gowenrw/3k_badge/docs/Code_01.JPG

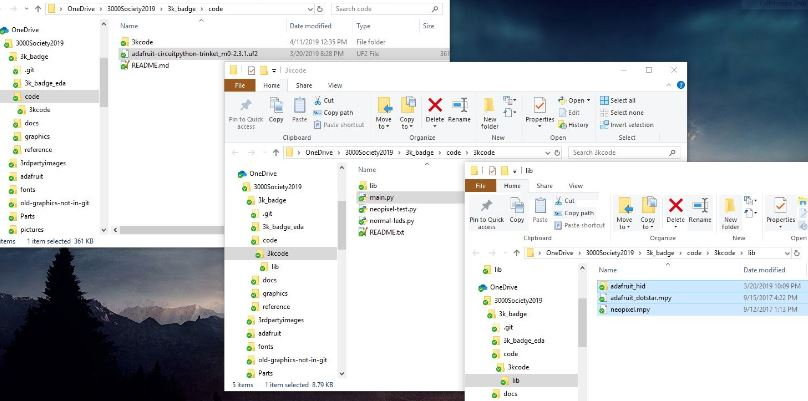
docs/Code_01.JPG
