gowenrw/3k_badge/docs/Code_04.JPG

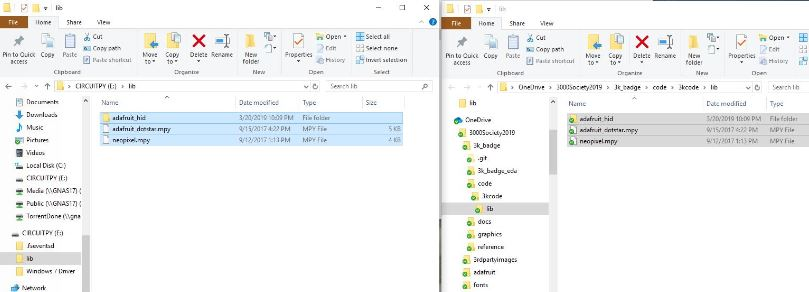
docs/Code_04.JPG
