gowenrw/3k_badge/docs/Code_05.JPG

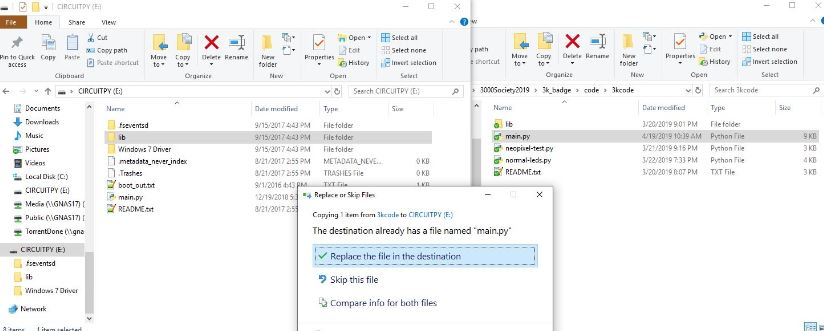
docs/Code_05.JPG
