gowenrw/3k_badge/graphics/3000-white-transparent-full-1080.png

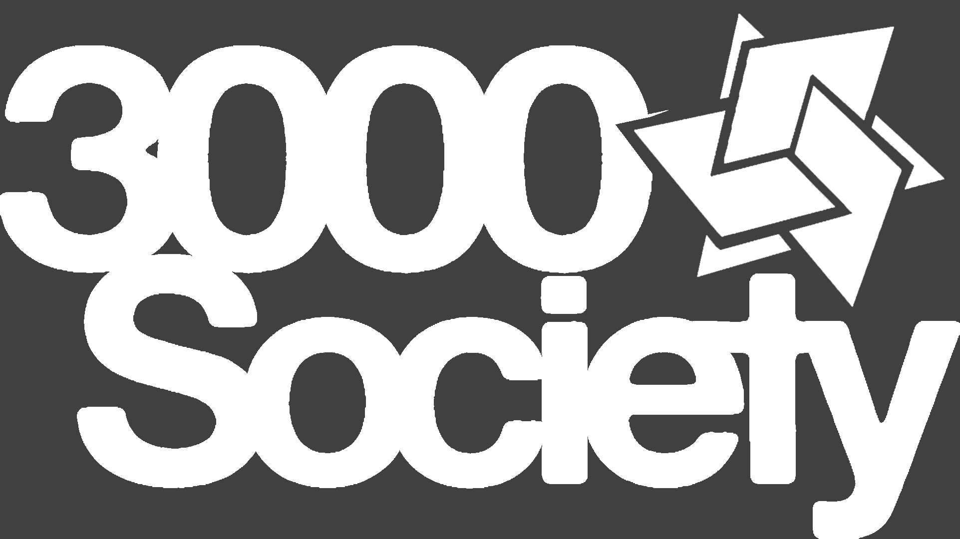
graphics/3000-white-transparent-full-1080.png
