gowenrw/3k_badge/graphics/DC214-a.png

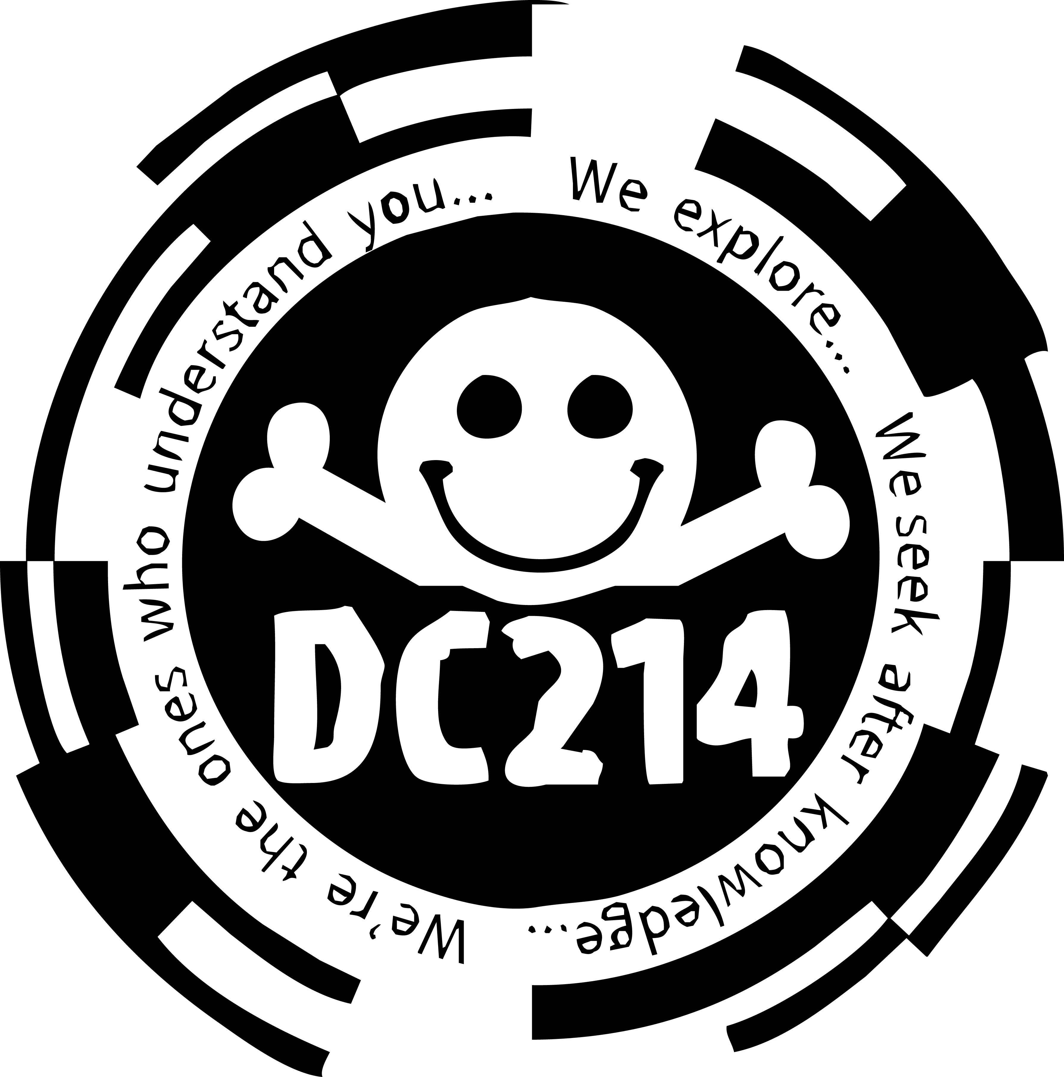
graphics/DC214-a.png
