gowenrw/3k_badge/graphics/DHA1.png

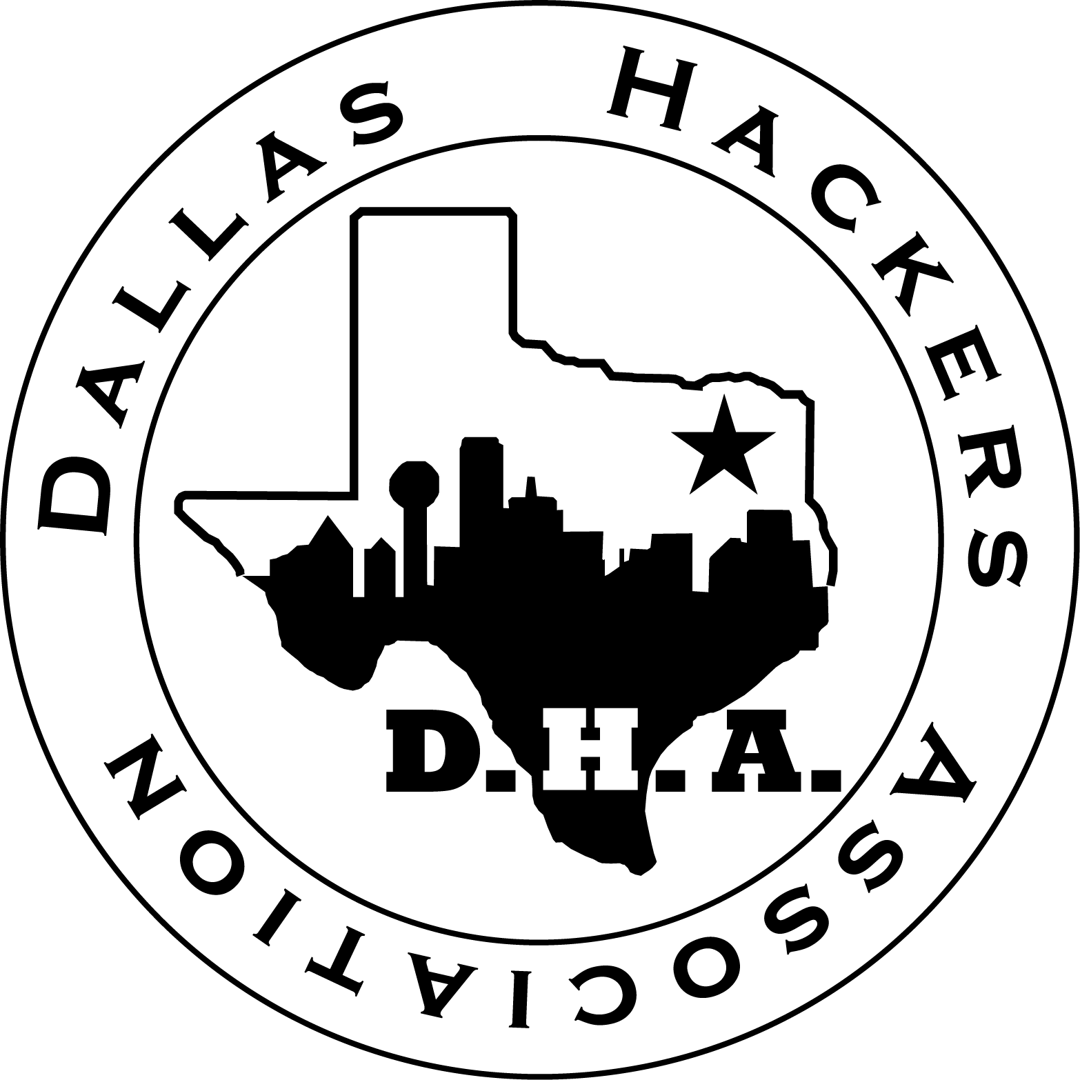
graphics/DHA1.png
