gowenrw/3k_badge/graphics/HackFtW1.png

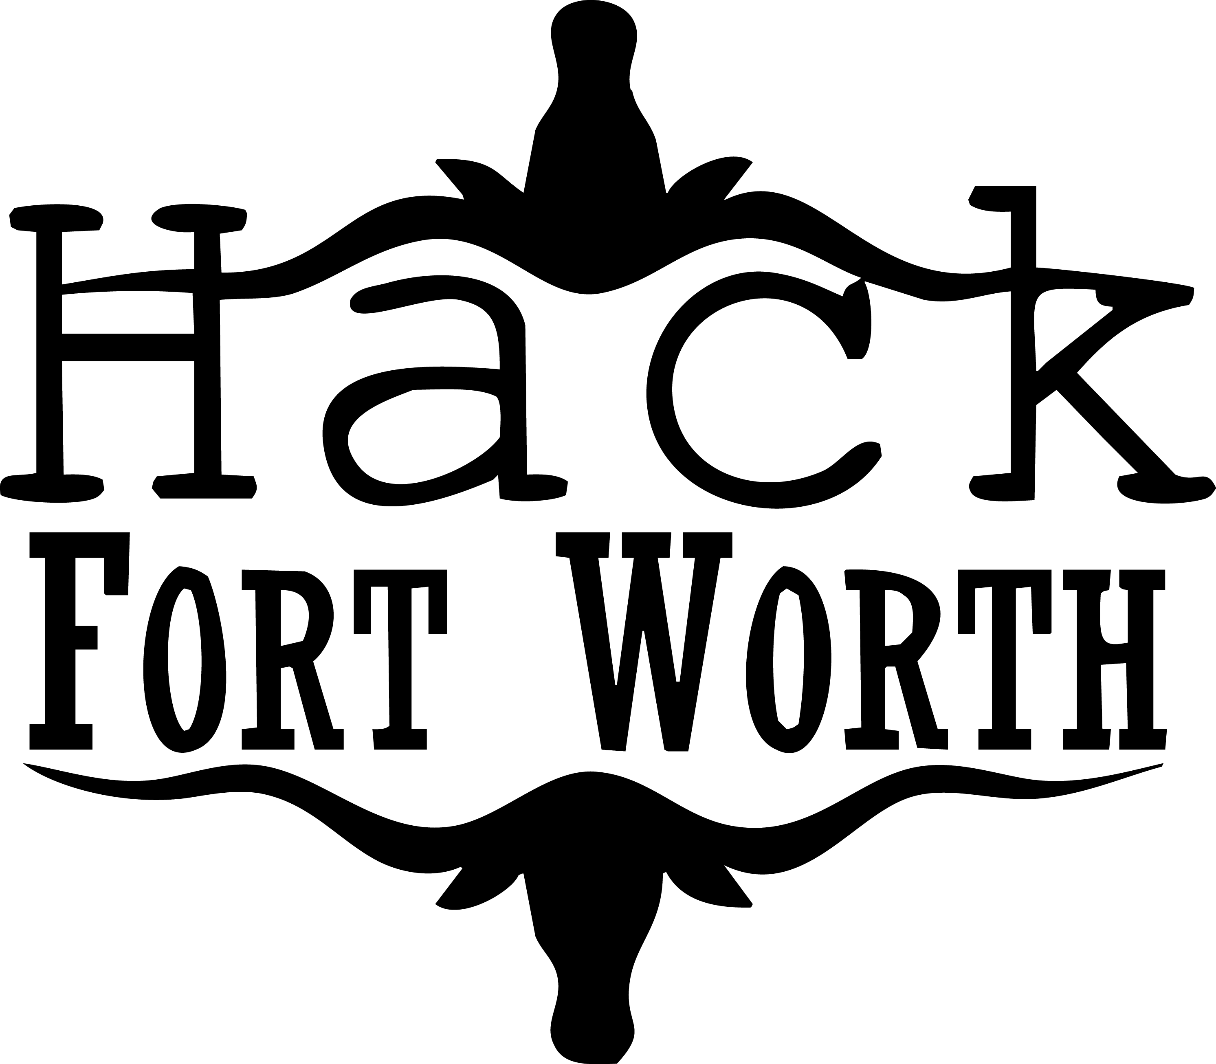
graphics/HackFtW1.png
