gowenrw/3k_badge/graphics/TheLab_ms_bw.png

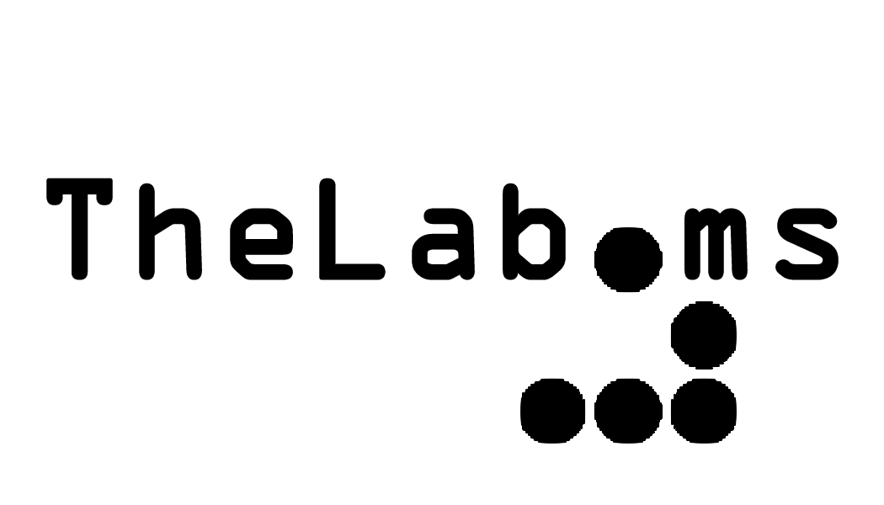
graphics/TheLab_ms_bw.png
