gowenrw/3k_badge/reference/trinket-m0/adafruit_products_fab_trinket_m0.png

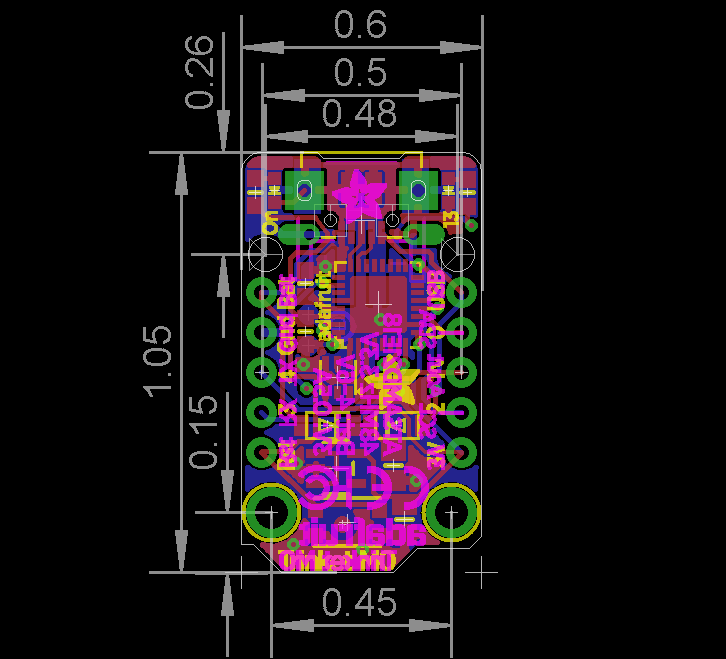
reference/trinket-m0/adafruit_products_fab_trinket_m0.png
