gowenrw/3k_badge/reference/trinket-m0/adafruit_products_schem_trinket_m0.png

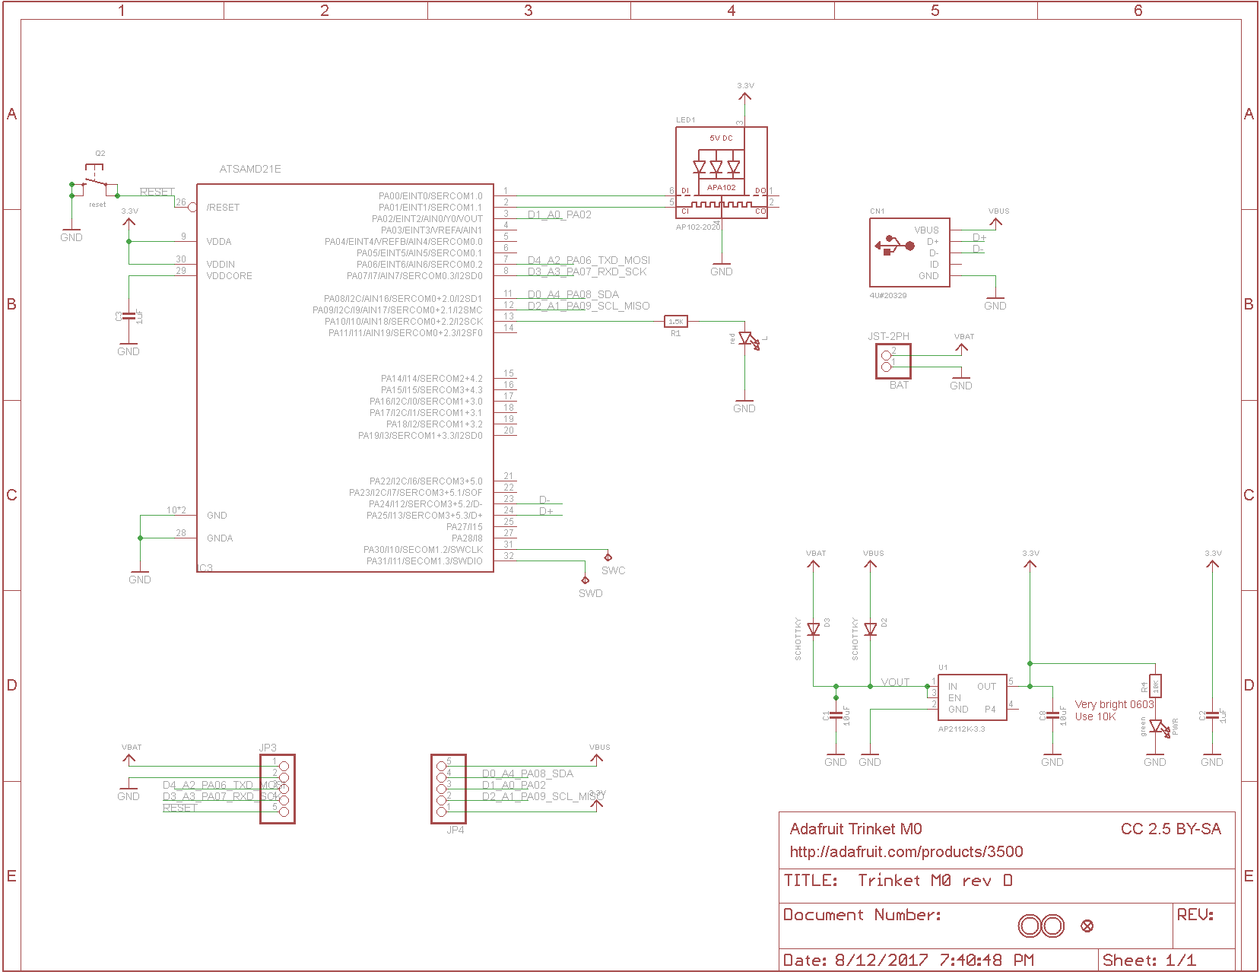
reference/trinket-m0/adafruit_products_schem_trinket_m0.png
